NewAmericanPublicArt/public-radio/resources/LinkSprite/Si4703_FM_BB_Sch.pdf

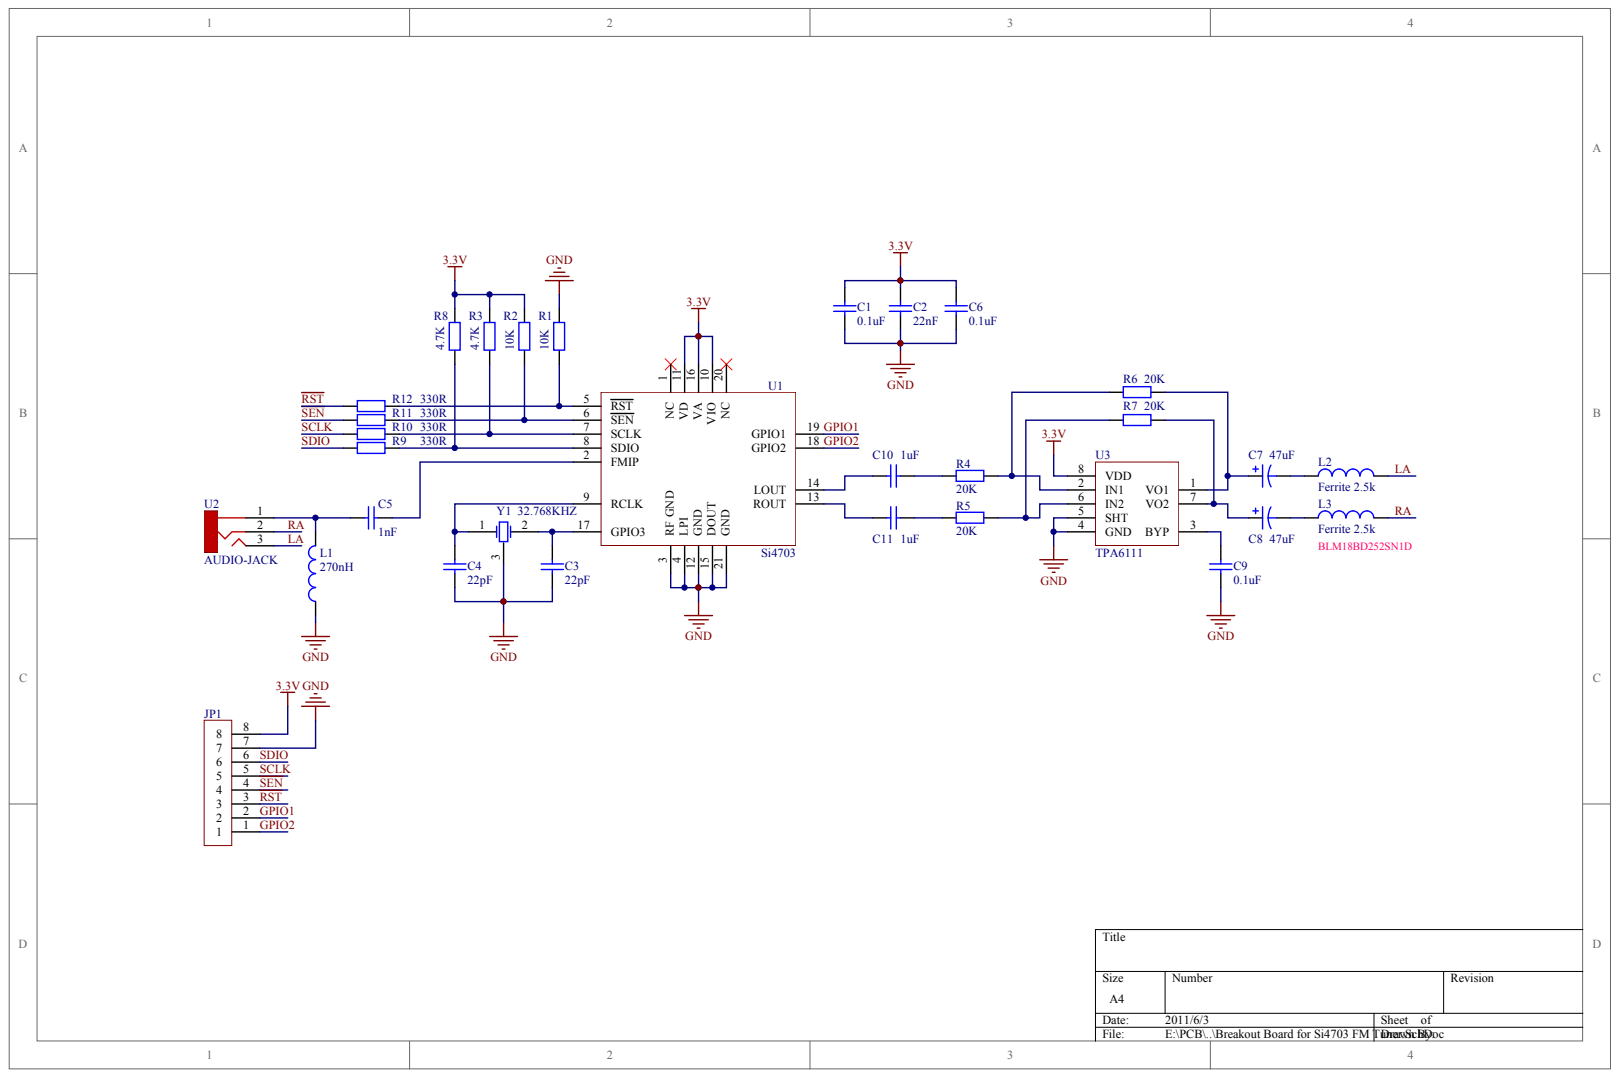
[picture p17: page 1]

GND 21 DOUT 15 GND 12 LPI 4 RF GND 3 NC 1

R9 330R | SDIO 8

FMIP 2

GPIO3 17
