NewAmericanPublicArt/public-radio/experiments/arduino-microbit/Blink/Blink.ino

// Getting started:
// Follow Microbit Arduino startup instructions: https://learn.adafruit.com/use-micro-bit-with-arduino/overview
//
// https://learn.adafruit.com/use-micro-bit-with-arduino/install-board-and-blink
// Simple Microbit test code for programming the Microbit
// using the Arduino IDE

const int COL1 = 3;     // Column #1 control
const int LED = 26;     // 'row 1' led

void setup() {  
  Serial.begin(9600);
  
  Serial.println("microbit is ready!");

  // because the LEDs are multiplexed, we must ground the opposite side of the LED
  pinMode(COL1, OUTPUT);
  digitalWrite(COL1, LOW); 
   
  pinMode(LED, OUTPUT);   
}

void loop(){
  Serial.println("blink!");
  
  digitalWrite(LED, HIGH);
  delay(500);
  digitalWrite(LED, LOW);
  delay(500);
}
